PR77/IoT_Messenger/Software/include/uiFrameSensor.h

#ifndef UI_FRAME_SENSOR
#define UI_FRAME_SENSOR

#include "Arduino.h"

#include <OLEDDisplay.h>
#include <OLEDDisplayFonts.h>
#include <OLEDDisplayUi.h>

//=============================================================================
// Prototypes
//=============================================================================

void uiFrameSensor(OLEDDisplay *display, OLEDDisplayUiState* state, int16_t x, int16_t y);

#endif // UI_FRAME_SENSOR
