PR77/IoT_Messenger/Software/src/uiFrameDino.cpp

#include "uiGlobal.h"
#include "uiFrameDino.h"

#include <ESP8266WiFi.h>

const uint8_t dinoLogo[] PROGMEM = {

    // https://www.dcode.fr/binary-image - LSB needs to be first in image data

    B00000000, B00000000, B00000000, B00000000, B00000000, B00000000, B00000000, B00001110, B00000000, B00000000, B00000000, B00000000, B00000000, B00000000, B00000000, B00000000,
    B00000000, B00000000, B00000000, B00000000, B00000000, B00000000, B10000000, B00110001, B00000000, B00000000, B00000000, B00000000, B00000000, B00000000, B00000000, B00000000,
    B00000000, B00000000, B00000000, B00000000, B00000000, B00000000, B01110000, B11000000, B00000000, B00000000, B00000000, B00000000, B00000000, B00000000, B00000000, B00000000,
    B00000000, B00000000, B00000000, B00000000, B00000000, B00000000, B00001000, B00000000, B00000001, B00000000, B00000000, B00000000, B00000000, B00000000, B00000000, B00000000,
    B00000000, B00000000, B00000000, B00000000, B00000000, B00000000, B11110000, B11111111, B00000001, B00000000, B10000000, B00000011, B00000000, B00000000, B00000000, B00000000,
    B00000000, B00000000, B00000000, B00000000, B00000011, B00000000, B00000000, B00000000, B00000000, B00000000, B01100000, B00001100, B00000000, B00000000, B00000000, B00000000,
    B00000000, B00000000, B11000000, B00000111, B00000011, B00000000, B00000000, B00000000, B00000000, B00000000, B00011100, B00110000, B00000000, B00000000, B00000000, B00000000,
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

};

void uiFrameDino(OLEDDisplay *display, OLEDDisplayUiState* state, int16_t x, int16_t y) {
    display->drawXbm(0 + x, 12 + y, 128, 20, dinoLogo);
}
