PR77/IoT_Messenger/Software/src/uiOverlay.cpp

#include "uiGlobal.h"
#include "uiOverlay.h"

#include <ESP8266WiFi.h>

//=============================================================================
// Message sprite
//=============================================================================

const uint8_t newMessage[] PROGMEM = {

    B11111111,
    B11000011,
    B10100101,
    B10011001,
    B10000001,
    B10000001,
    B11111111,
};

//=============================================================================
// Wifi sprite
//=============================================================================

const uint8_t wifiConnected[] PROGMEM = {

    B00111100,
    B11000011,
    B00111100,
    B01000010,
    B00011000,
    B00100100,
    B00011000,
};

void uiOverlay(OLEDDisplay *display, OLEDDisplayUiState* state) {
    String overlayText = String();

    display->setTextAlignment(TEXT_ALIGN_RIGHT);
    display->setFont(ArialMT_Plain_10);

    overlayText = "vBatt: ";
    overlayText += ((analogRead(A0) / 1023.0) * 4.43);
    overlayText += "V, UiFrm: ";
    overlayText += state->currentFrame;

    display->drawString(128, 0, overlayText);

    if (WiFi.status() == WL_CONNECTED) {
        display->drawXbm(0, 2, 8, 7, wifiConnected);
    }

    if ((*(uiGlobalObject_s *)(state->userData)).messageObject_p->newMessageReceived == true) {
        display->drawXbm(11, 2, 8, 7, newMessage);
    }
}
